habworks/Softcore_SA_P2/Simulation/SPICE/Sallen & Key LPF.asc

C1: cap; 200e-12
C2: cap; 100e-12
C3: cap; 100e-12
C4: cap; 200e-12
D1: diode; 1N4148
D2: diode; 1N4148
R1: res; 220
R2: res; 220
R3: res; 440
R4: res; 100
R5: res; 1K
R6: res; 440
R7: res; 220
R8: res; 220
R10: res; 1K
R11: res; 100
U1: LT1818
U2: ADA4896-2
U3: LT1818
V1: voltage; 3.3V
V2: voltage; SINE(.344 .306 1E5 0 0 0 50); AC 1
V3: voltage; 1.5V
V4: voltage; 1V
Named nets: 0, VCC, VIN, VBUF, VOUT, VOUT_2, VTEST
;tran 10e-5
.ac dec 100 100 10e6
R3 and R6 can be their value or 0.  When sum of input resistors a balance of the input impedance to both + / - terminals.
Otherwise it does not play into circuit calculation
w = 2piF = 1 / SQRT(R1*R2*C1*C2)
Q = SQRT(R1*R2*C1*C2) / (C2(R1 + R2))
Per Stage -40dB/Decade
Per Q = 0.707
Total Roll Off -80dB/Decade
voltage noise per stage = 2.44uV @5MHz
cumulative voltage noise - vector sum = 3.87uV @5MHz
U2 ADA4896 has a wider input Common Mode Voltage range.  
U1 and U3 are cheaper componets but still have a large GBP necessary for filter operation
