habworks/Softcore_SA_P2/Simulation/SPICE/Wien_Bridge_Offset.asc

C1: cap; {Cw}
C2: cap; {Cw}
C3: cap; 10µF
D1: diode; 1N4148
D2: diode; 1N4148
D3: diode; 1N4148
D4: diode; 1N4148
R1: res; 22K
R2: res; {Rw}
R3: res; {Rw}
R4: res; 10K
R5: res; 22K
R6: res; 10K
R7: res; 10K
R8: res; 10K
R9: res; 10K
R10: res; 10K
R11: res; 10K
R12: res; 10K
R13: res; 2.5K
R14: res; 7.5K
R15: res; 10K
U1: ADA4896-2
U2: ADA4896-2
U3: ADA4896-2
U4: AD8606
V1: voltage; 5
V2: voltage; -5
V3: voltage; PULSE(0 .5E-3 0 1E-9 1E-9 1E-4 1E+6 1)
Named nets: VCC, 0, VO_1, VEE, VO_2
.tran 100e-6 uic
.param Rw=200
.param Cw=160pF
V3 is a pulse - necessary to get the ossiclation going.  It would not 
be necessary in a real circuit, but is necessary in a mathematical model due to 
Op Amp modeled too ideal
Capacitors should be ceramic of COG, NP0 type for stability
AD8608 x4 Op Amps
AD8606 x2 Op Amps
AD8605 x1 Op Amp
Double diodes in circuit work to limit out to 2x Vd.  On diode condution R5 in parallel with
R1 to limit gain.  This type of ossicaltor requires a gain of 3 to work.  Without diode circuit
in feedback the ouput would swing to the rails and be clipped creating harmonics
F = 1 / (2*PI*Rw*Cw)
At R = 11K Frequency = 4.384KHz
At R = 1K Frequency = 48.22KHz
.four 48.22k V(VO_2)
AC Analysis - must have:
FFT Analysis done after transient analysis - go to transisent graph and View > FFT
