habworks/Softcore_SA_P2/Simulation/SPICE/Quadrature_Oscillator.asc

C2: cap; .01µF
C3: cap; .01µF
C4: cap; .01µF
R1: res; 100K
R2: res; 100K
R3: res; 100K
R4: res; 100K
U1: TLV9302
U2: TLV9302
V1: voltage; 10
V2: voltage; -10
Named nets: VCC, 0, VOUT, VEE
.tran .2
