habworks/Softcore_SA_P2/Simulation/SPICE/Sallen & Key LPF_Transient.asc

C1: cap; 220e-12
C2: cap; 470e-12
D1: diode; 1N4148
D2: diode; 1N4148
R1: res; 1.5K
R2: res; 1.5K
R3: res; 3K
R4: res; 1K
R5: res; 1K
U1: AD8606
U3: AD8606
V1: voltage; 3.3V
V2: voltage; SINE(1.5 1.5 20e2 0 0 0 10); AC 1
Named nets: 0, VCC, VIN, VOUT
.tran .01
;ac dec 1000 10 2e6
R3 can be 2K or 0.  When 2K it forms a balance of the input impedance to both + / - terminals.
Otherwise it does not play into circuit calculation
w = 2piF = 1 / SQRT(R1*R2*C1*C2)
Q = SQRT(R1*R2*C1*C2) / (C2(R1 + R2)
Reference: https://circuitcellar.com/resources/quickbits/sallen-n-key-filter/
Gain at frequency f
G(f) = 1 / SQRT(1 + f/fc)^2n)
fc = cutoff frequency
n = number of poles (Sallen & Key has 2 poles)
