habworks/Softcore_SA_P2/PS_Softcore_SA/MB_SSA_Platform/microblaze_0/standalone_microblaze_0/bsp/include/xparameters.h

#ifndef XPARAMETERS_H   /* prevent circular inclusions */
#define XPARAMETERS_H   /* by using protection macros */

#define XPAR_XGPIO_NUM_INSTANCES 1

/* Definitions for peripheral AXI_GPIO_0 */
#define XPAR_AXI_GPIO_0_COMPATIBLE "xlnx,axi-gpio-2.0"
#define XPAR_AXI_GPIO_0_BASEADDR 0x40000000
#define XPAR_AXI_GPIO_0_HIGHADDR 0x4000ffff
#define XPAR_AXI_GPIO_0_INTERRUPT_PRESENT 0x0
#define XPAR_AXI_GPIO_0_IS_DUAL 0x1
#define XPAR_AXI_GPIO_0_GPIO_WIDTH 0xc

/* Canonical definitions for peripheral AXI_GPIO_0 */
#define XPAR_XGPIO_0_BASEADDR 0x40000000
#define XPAR_XGPIO_0_HIGHADDR 0x4000ffff
#define XPAR_XGPIO_0_COMPATIBLE "xlnx,axi-gpio-2.0"
#define XPAR_XGPIO_0_GPIO_WIDTH 0xc
#define XPAR_XGPIO_0_INTERRUPT_PRESENT 0x0
#define XPAR_XGPIO_0_IS_DUAL 0x1

#define XPAR_XINTC_NUM_INSTANCES 1

/* Definitions for peripheral AXI_INTC_0 */
#define XPAR_AXI_INTC_0_COMPATIBLE "xlnx,axi-intc-4.1"
#define XPAR_AXI_INTC_0_BASEADDR 0x41200000
#define XPAR_AXI_INTC_0_HIGHADDR 0x4120ffff
#define XPAR_AXI_INTC_0_KIND_OF_INTR 0xf
#define XPAR_AXI_INTC_0_IS_FAST 0x1
#define XPAR_AXI_INTC_0_IVAR_RST_VAL 0x10
#define XPAR_AXI_INTC_0_NUM_INTR_INPUTS 0x4
#define XPAR_AXI_INTC_0_ADDR_WIDTH 0x20
#define XPAR_AXI_INTC_0_OPTIONS 0x0
#define XPAR_AXI_INTC_0_INTCTYPE 0x0
#define XPAR_AXI_INTC_0_HANDLER_TABLE 0x0
#define XPAR_AXI_INTC_0_NUM_SW_INTR 0x0

/* Canonical definitions for peripheral AXI_INTC_0 */
#define XPAR_XINTC_0_BASEADDR 0x41200000
#define XPAR_XINTC_0_HIGHADDR 0x4120ffff
#define XPAR_XINTC_0_HANDLER_TABLE 0x0
#define XPAR_XINTC_0_ADDR_WIDTH 0x20
#define XPAR_XINTC_0_COMPATIBLE "xlnx,axi-intc-4.1"
#define XPAR_XINTC_0_IS_FAST 0x1
#define XPAR_XINTC_0_IVAR_RST_VAL 0x10
#define XPAR_XINTC_0_INTCTYPE 0x0
#define XPAR_XINTC_0_KIND_OF_INTR 0xf
#define XPAR_XINTC_0_NUM_INTR_INPUTS 0x4
#define XPAR_XINTC_0_NUM_SW_INTR 0x0
#define XPAR_XINTC_0_OPTIONS 0x0

#define XPAR_XSPI_NUM_INSTANCES 3

/* Definitions for peripheral AXI_QUAD_SPI_0 */
#define XPAR_AXI_QUAD_SPI_0_COMPATIBLE "xlnx,axi-quad-spi-3.2"
#define XPAR_AXI_QUAD_SPI_0_BASEADDR 0x44a10000
#define XPAR_AXI_QUAD_SPI_0_HIGHADDR 0x44a1ffff
#define XPAR_AXI_QUAD_SPI_0_HASFIFOS 0x1
#define XPAR_AXI_QUAD_SPI_0_SLAVEONLY 0x0
#define XPAR_AXI_QUAD_SPI_0_NUM_SS_BITS 0x4
#define XPAR_AXI_QUAD_SPI_0_BITS_PER_WORD 0x8
#define XPAR_AXI_QUAD_SPI_0_SPI_MODE 0x0
#define XPAR_AXI_QUAD_SPI_0_AXI_INTERFACE 0x0
#define XPAR_AXI_QUAD_SPI_0_AXI4_ADDRESS 0x0
#define XPAR_AXI_QUAD_SPI_0_XIP_MODE 0x0
#define XPAR_AXI_QUAD_SPI_0_STARTUP_BLOCK 0x0
#define XPAR_AXI_QUAD_SPI_0_FIFO_SIZE 0x10

/* Canonical definitions for peripheral AXI_QUAD_SPI_0 */
#define XPAR_XSPI_0_AXI4_ADDRESS 0x0
#define XPAR_XSPI_0_BASEADDR 0x44a10000
#define XPAR_XSPI_0_HIGHADDR 0x44a1ffff
#define XPAR_XSPI_0_AXI_INTERFACE 0x0
#define XPAR_XSPI_0_BITS_PER_WORD 0x8
#define XPAR_XSPI_0_COMPATIBLE "xlnx,axi-quad-spi-3.2"
#define XPAR_XSPI_0_FIFO_SIZE 0x10
#define XPAR_XSPI_0_HASFIFOS 0x1
#define XPAR_XSPI_0_NUM_SS_BITS 0x4
#define XPAR_XSPI_0_SLAVEONLY 0x0
#define XPAR_XSPI_0_SPI_MODE 0x0
#define XPAR_XSPI_0_STARTUP_BLOCK 0x0
#define XPAR_XSPI_0_XIP_MODE 0x0

/* Definitions for peripheral AXI_QUAD_SPI_1 */
#define XPAR_AXI_QUAD_SPI_1_COMPATIBLE "xlnx,axi-quad-spi-3.2"
#define XPAR_AXI_QUAD_SPI_1_BASEADDR 0x44a00000
#define XPAR_AXI_QUAD_SPI_1_HIGHADDR 0x44a0ffff
#define XPAR_AXI_QUAD_SPI_1_HASFIFOS 0x1
#define XPAR_AXI_QUAD_SPI_1_SLAVEONLY 0x0
#define XPAR_AXI_QUAD_SPI_1_NUM_SS_BITS 0x1
#define XPAR_AXI_QUAD_SPI_1_BITS_PER_WORD 0x8
#define XPAR_AXI_QUAD_SPI_1_SPI_MODE 0x0
#define XPAR_AXI_QUAD_SPI_1_AXI_INTERFACE 0x0
#define XPAR_AXI_QUAD_SPI_1_AXI4_ADDRESS 0x0
#define XPAR_AXI_QUAD_SPI_1_XIP_MODE 0x0
#define XPAR_AXI_QUAD_SPI_1_STARTUP_BLOCK 0x0
#define XPAR_AXI_QUAD_SPI_1_FIFO_SIZE 0x10

/* Canonical definitions for peripheral AXI_QUAD_SPI_1 */
#define XPAR_XSPI_1_AXI4_ADDRESS 0x0
#define XPAR_XSPI_1_BASEADDR 0x44a00000
#define XPAR_XSPI_1_HIGHADDR 0x44a0ffff
#define XPAR_XSPI_1_AXI_INTERFACE 0x0
#define XPAR_XSPI_1_BITS_PER_WORD 0x8
#define XPAR_XSPI_1_COMPATIBLE "xlnx,axi-quad-spi-3.2"
#define XPAR_XSPI_1_FIFO_SIZE 0x10
#define XPAR_XSPI_1_HASFIFOS 0x1
#define XPAR_XSPI_1_NUM_SS_BITS 0x1
#define XPAR_XSPI_1_SLAVEONLY 0x0
#define XPAR_XSPI_1_SPI_MODE 0x0
#define XPAR_XSPI_1_STARTUP_BLOCK 0x0
#define XPAR_XSPI_1_XIP_MODE 0x0

/* Definitions for peripheral AXI_QUAD_SPI_2 */
#define XPAR_AXI_QUAD_SPI_2_COMPATIBLE "xlnx,axi-quad-spi-3.2"
#define XPAR_AXI_QUAD_SPI_2_BASEADDR 0x44a40000
#define XPAR_AXI_QUAD_SPI_2_HIGHADDR 0x44a4ffff
#define XPAR_AXI_QUAD_SPI_2_HASFIFOS 0x1
#define XPAR_AXI_QUAD_SPI_2_SLAVEONLY 0x0
#define XPAR_AXI_QUAD_SPI_2_NUM_SS_BITS 0x1
#define XPAR_AXI_QUAD_SPI_2_BITS_PER_WORD 0x8
#define XPAR_AXI_QUAD_SPI_2_SPI_MODE 0x2
#define XPAR_AXI_QUAD_SPI_2_AXI_INTERFACE 0x0
#define XPAR_AXI_QUAD_SPI_2_AXI4_ADDRESS 0x0
#define XPAR_AXI_QUAD_SPI_2_XIP_MODE 0x0
#define XPAR_AXI_QUAD_SPI_2_STARTUP_BLOCK 0x1
#define XPAR_AXI_QUAD_SPI_2_FIFO_SIZE 0x10

/* Canonical definitions for peripheral AXI_QUAD_SPI_2 */
#define XPAR_XSPI_2_AXI4_ADDRESS 0x0
#define XPAR_XSPI_2_BASEADDR 0x44a40000
#define XPAR_XSPI_2_HIGHADDR 0x44a4ffff
#define XPAR_XSPI_2_AXI_INTERFACE 0x0
#define XPAR_XSPI_2_BITS_PER_WORD 0x8
#define XPAR_XSPI_2_COMPATIBLE "xlnx,axi-quad-spi-3.2"
#define XPAR_XSPI_2_FIFO_SIZE 0x10
#define XPAR_XSPI_2_HASFIFOS 0x1
#define XPAR_XSPI_2_NUM_SS_BITS 0x1
#define XPAR_XSPI_2_SLAVEONLY 0x0
#define XPAR_XSPI_2_SPI_MODE 0x2
#define XPAR_XSPI_2_STARTUP_BLOCK 0x1
#define XPAR_XSPI_2_XIP_MODE 0x0

#define XPAR_XTMRCTR_NUM_INSTANCES 4

/* Definitions for peripheral AXI_TIMER_0 */
#define XPAR_AXI_TIMER_0_COMPATIBLE "xlnx,axi-timer-2.0"
#define XPAR_AXI_TIMER_0_BASEADDR 0x41c00000
#define XPAR_AXI_TIMER_0_HIGHADDR 0x41c0ffff
#define XPAR_AXI_TIMER_0_CLOCK_FREQUENCY 0x5f5e100

/* Canonical definitions for peripheral AXI_TIMER_0 */
#define XPAR_XTMRCTR_0_BASEADDR 0x41c00000
#define XPAR_XTMRCTR_0_HIGHADDR 0x41c0ffff
#define XPAR_XTMRCTR_0_COMPATIBLE "xlnx,axi-timer-2.0"
#define XPAR_XTMRCTR_0_CLOCK_FREQUENCY 0x5f5e100

/* Definitions for peripheral AXI_TIMER_1 */
#define XPAR_AXI_TIMER_1_COMPATIBLE "xlnx,axi-timer-2.0"
#define XPAR_AXI_TIMER_1_BASEADDR 0x41c10000
#define XPAR_AXI_TIMER_1_HIGHADDR 0x41c1ffff
#define XPAR_AXI_TIMER_1_CLOCK_FREQUENCY 0x5f5e100
#define XPAR_AXI_TIMER_1_INTERRUPTS 0x2000
#define XPAR_FABRIC_AXI_TIMER_1_INTR 0
#define XPAR_AXI_TIMER_1_INTERRUPT_PARENT 0x41200001

/* Canonical definitions for peripheral AXI_TIMER_1 */
#define XPAR_XTMRCTR_1_BASEADDR 0x41c10000
#define XPAR_FABRIC_XTMRCTR_1_INTR 0
#define XPAR_XTMRCTR_1_HIGHADDR 0x41c1ffff
#define XPAR_XTMRCTR_1_COMPATIBLE "xlnx,axi-timer-2.0"
#define XPAR_XTMRCTR_1_CLOCK_FREQUENCY 0x5f5e100
#define XPAR_XTMRCTR_1_INTERRUPTS 0x2000
#define XPAR_XTMRCTR_1_INTERRUPT_PARENT 0x41200001

/* Definitions for peripheral AXI_TIMER_2 */
#define XPAR_AXI_TIMER_2_COMPATIBLE "xlnx,axi-timer-2.0"
#define XPAR_AXI_TIMER_2_BASEADDR 0x41c20000
#define XPAR_AXI_TIMER_2_HIGHADDR 0x41c2ffff
#define XPAR_AXI_TIMER_2_CLOCK_FREQUENCY 0x5f5e100
#define XPAR_AXI_TIMER_2_INTERRUPTS 0x2001
#define XPAR_FABRIC_AXI_TIMER_2_INTR 1
#define XPAR_AXI_TIMER_2_INTERRUPT_PARENT 0x41200001

/* Canonical definitions for peripheral AXI_TIMER_2 */
#define XPAR_XTMRCTR_2_BASEADDR 0x41c20000
#define XPAR_FABRIC_XTMRCTR_2_INTR 1
#define XPAR_XTMRCTR_2_HIGHADDR 0x41c2ffff
#define XPAR_XTMRCTR_2_COMPATIBLE "xlnx,axi-timer-2.0"
#define XPAR_XTMRCTR_2_CLOCK_FREQUENCY 0x5f5e100
#define XPAR_XTMRCTR_2_INTERRUPTS 0x2001
#define XPAR_XTMRCTR_2_INTERRUPT_PARENT 0x41200001

/* Definitions for peripheral AXI_TIMER_3 */
#define XPAR_AXI_TIMER_3_COMPATIBLE "xlnx,axi-timer-2.0"
#define XPAR_AXI_TIMER_3_BASEADDR 0x41c30000
#define XPAR_AXI_TIMER_3_HIGHADDR 0x41c3ffff
#define XPAR_AXI_TIMER_3_CLOCK_FREQUENCY 0x5f5e100

/* Canonical definitions for peripheral AXI_TIMER_3 */
#define XPAR_XTMRCTR_3_BASEADDR 0x41c30000
#define XPAR_XTMRCTR_3_HIGHADDR 0x41c3ffff
#define XPAR_XTMRCTR_3_COMPATIBLE "xlnx,axi-timer-2.0"
#define XPAR_XTMRCTR_3_CLOCK_FREQUENCY 0x5f5e100

#define XPAR_XUARTLITE_NUM_INSTANCES 1

/* Definitions for peripheral AXI_UARTLITE_0 */
#define XPAR_AXI_UARTLITE_0_COMPATIBLE "xlnx,axi-uartlite-2.0"
#define XPAR_AXI_UARTLITE_0_BASEADDR 0x40600000
#define XPAR_AXI_UARTLITE_0_HIGHADDR 0x4060ffff
#define XPAR_AXI_UARTLITE_0_BAUDRATE 0x1c200
#define XPAR_AXI_UARTLITE_0_USE_PARITY 0x0
#define XPAR_AXI_UARTLITE_0_ODD_PARITY 0x0
#define XPAR_AXI_UARTLITE_0_DATA_BITS 0x8

/* Canonical definitions for peripheral AXI_UARTLITE_0 */
#define XPAR_XUARTLITE_0_BASEADDR 0x40600000
#define XPAR_XUARTLITE_0_HIGHADDR 0x4060ffff
#define XPAR_XUARTLITE_0_BAUDRATE 0x1c200
#define XPAR_XUARTLITE_0_COMPATIBLE "xlnx,axi-uartlite-2.0"
#define XPAR_XUARTLITE_0_DATA_BITS 0x8
#define XPAR_XUARTLITE_0_ODD_PARITY 0x0
#define XPAR_XUARTLITE_0_USE_PARITY 0x0

/* Definitions for peripheral IMR_ADC_7476A_X2_0 */
#define XPAR_IMR_ADC_7476A_X2_0_BASEADDR 0x44a30000
#define XPAR_IMR_ADC_7476A_X2_0_HIGHADDR 0x44a3ffff

/* Canonical definitions for peripheral IMR_ADC_7476A_X2_0 */
#define XPAR_IMR_ADC_7476A_X2_0_BASEADDR 0x44a30000
#define XPAR_IMR_ADC_7476A_X2_0_HIGHADDR 0x44a3ffff

/* Definitions for peripheral IMR_PL_REVISION_0 */
#define XPAR_IMR_PL_REVISION_0_BASEADDR 0x44a20000
#define XPAR_IMR_PL_REVISION_0_HIGHADDR 0x44a2ffff

/* Canonical definitions for peripheral IMR_PL_REVISION_0 */
#define XPAR_IMR_PL_REVISION_0_BASEADDR 0x44a20000
#define XPAR_IMR_PL_REVISION_0_HIGHADDR 0x44a2ffff

#define XPAR_MIG_0_BASEADDRESS 0x80000000
#define XPAR_MIG_0_HIGHADDRESS 0x8fffffff
#define XPAR_LMB_BRAM_0_BASEADDRESS 0x0
#define XPAR_LMB_BRAM_0_HIGHADDRESS 0x1ffff
#define XPAR_CPU_CORE_CLOCK_FREQ_HZ 100000000

#define XPAR_MICROBLAZE_ADDR_SIZE 32

#define XPAR_MICROBLAZE_USE_STACK_PROTECTION 0

/* Number of SLRs */
#define NUMBER_OF_SLRS 0x1

/* Device ID */
#define XPAR_DEVICE_ID "7a100t"

#endif  /* end of protection macro */
