habworks/Softcore_SA_P2/PL_Softcore_SA/PL_Softcore_SA.srcs/sources_1/new/Top.v

`timescale 1ns / 1ps
//////////////////////////////////////////////////////////////////////////////////
// Company: 
// Engineer: 
// 
// Create Date: 12/05/2025 05:24:13 AM
// Design Name: 
// Module Name: Top
// Project Name: 
// Target Devices: 
// Tool Versions: 
// Description: 
// 
// Dependencies: 
// 
// Revision:
// Revision 0.01 - File Created
// Additional Comments:
// 
//////////////////////////////////////////////////////////////////////////////////


module Top(

    );
endmodule
