habworks/Softcore_SA_P2/PS_Softcore_SA/MB_SSA_App/src/Main_Support.h

/******************************************************************************************************
 * @file            Main_Support.h
 * @brief           Header file to support Main_Support.c 
 * ****************************************************************************************************
 * @author          Hab Collector (habco)\n
 *
 * @version         See Main_Support.h: FW_MAJOR_REV, FW_MINOR_REV, FW_TEST_REV
 *
 * @param Development_Environment \n
 * Hardware:        <Xilinx Artix A7> \n
 * IDE:             Vitis 2024.2 \n
 * Compiler:        GCC \n
 * Editor Settings: 1 Tab = 4 Spaces, Recommended Courier New 11
 *
 * @note            The associated header file provides MACRO functions for IO control
 *
 *                  This is an embedded application
 *                  It will be necessary to consult the reference documents to fully understand the code
 *                  It is suggested that the documents be reviewed in the order shown.
 *                    Schematic: 
 *                    IMR Engineering
 *                    IMR Engineering
 *
 * @copyright       IMR Engineering, LLC
 ********************************************************************************************************/

#ifndef MAIN_SUPPORT_H_
#define MAIN_SUPPORT_H_
#ifdef __cplusplus
extern"C" {
#endif

#include <stdint.h>
#include <stdbool.h>
#include <xparameters.h>
#include "xtmrctr.h"
#include "SSD1309_Driver.h"
#include "kiss_fftr.h"


// DEFINES
// PS FW REVSION
#define FW_MAJOR_REV            1
#define FW_MINOR_REV            2
#define FW_TEST_REV             1
#define HW_REV                  1 
// UART USE
#define RX_BUFFER_SIZE          10  
// MICROBLAZE CACHE SUPPORT *** THESE LINES SHOULD BE ADDED WITHIN XPARAMETERS.H BUT THERE IS A BUG IN 2024.2 Vivado / Viits
#define XPAR_MICROBLAZE_USE_ICACHE      1
#define XPAR_MICROBLAZE_USE_DCACHE      1
#define XPAR_MICROBLAZE_USE_MSR_INSTR   1
#define XPAR_MICROBLAZE_ICACHE_BYTE_SIZE 65536  // Value must match MicroBlaze Instruction cache
#define XPAR_MICROBLAZE_DCACHE_BYTE_SIZE 32768  // Value must match MicroBlaze Data cache
// AXI SPI UI CHIP SELECT
#define DISPLAY_CS_NUMBER       ((uint8_t)(0x01 << 0))
#define IOX_1_CS_NUMBER         ((uint8_t)(0x01 << 1))
#define IOX_2_CS_NUMBER         ((uint8_t)(0x01 << 2))
#define AD9833_CS_NUMBER        ((uint8_t)(0x01 << 3))
// IO EXPANDER 1 CONFIGURATION
#define IOX_1_DEVICE_ADDR       ((uint8_t)(0x00))
#define IOX_1_IO_DIRECTION      ((uint8_t)(0x00))
#define IOX_1_INPUT_POLARITY    ((uint8_t)(0x00))
#define IOX_1_IRQ_ON_CHANGE     ((uint8_t)(0x00))
#define IOX_1_IRQ_DEFAULT_VALUE ((uint8_t)(0x00))
#define IOX_1_IRQ_CONTROL       ((uint8_t)(0x00))
#define IOX_1_CONFIGURATION     MCP23S08_SEQOP_BIT_MASK
#define IOX_1_PULLUP            ((uint8_t)(0x00))
// IO EXPANDER 2 CONFIGURATION
#define IOX_2_DEVICE_ADDR       ((uint8_t)(0x01))
#define IOX_2_IO_DIRECTION      ((uint8_t)(0xFF))
#define IOX_2_INPUT_POLARITY    ((uint8_t)(0xC0))   // Two most MSb inputs are active low - so invert
#define IOX_2_IRQ_ON_CHANGE     ((uint8_t)(0xFF))
#define IOX_2_IRQ_DEFAULT_VALUE ((uint8_t)(0x00))
#define IOX_2_IRQ_CONTROL       ((uint8_t)(0x00))
#define IOX_2_CONFIGURATION     (MCP23S08_SEQOP_BIT_MASK | MCP23S08_INTPOL_BIT_MASK)
#define IOX_2_PULLUP            ((uint8_t)(0x00))
// IO EXPANDER 1 OUTPUTS AND ALIAS
#define IOX_1_OUTPUT_0_MASK     ((uint8_t)(0x01 << 0))
#define IOX_1_OUTPUT_1_MASK     ((uint8_t)(0x01 << 1))
#define IOX_1_OUTPUT_2_MASK     ((uint8_t)(0x01 << 2))
#define IOX_1_OUTPUT_3_MASK     ((uint8_t)(0x01 << 3))
#define IOX_1_OUTPUT_4_MASK     ((uint8_t)(0x01 << 4))
#define IOX_1_OUTPUT_5_MASK     ((uint8_t)(0x01 << 5))
#define IOX_1_OUTPUT_6_MASK     ((uint8_t)(0x01 << 6))
#define IOX_1_OUTPUT_7_MASK     ((uint8_t)(0x01 << 7))
#define LED_MODE_SIGNAL         ((uint8_t)(0x01 << 6))
#define LED_MODE_AUDIO          ((uint8_t)(0x01 << 7))
// IO EXPANDER 2 INPUTS AND ALIAS
#define IOX_2_INPUT_0_MASK      ((uint8_t)(0x01 << 0))
#define IOX_2_INPUT_1_MASK      ((uint8_t)(0x01 << 1))
#define IOX_2_INPUT_2_MASK      ((uint8_t)(0x01 << 2))
#define IOX_2_INPUT_3_MASK      ((uint8_t)(0x01 << 3))
#define IOX_2_INPUT_4_MASK      ((uint8_t)(0x01 << 4))
#define IOX_2_INPUT_5_MASK      ((uint8_t)(0x01 << 5))
#define IOX_2_INPUT_6_MASK      ((uint8_t)(0x01 << 6))
#define IOX_2_INPUT_7_MASK      ((uint8_t)(0x01 << 7))
#define UI_SW6_PLAY_HOME        IOX_2_INPUT_0_MASK
#define UI_SW5_PAUSE_AF_TOGGLE  IOX_2_INPUT_1_MASK
#define UI_SW4_STOP_SPAN_TOGGLE IOX_2_INPUT_2_MASK
#define UI_SW3_SELECT           IOX_2_INPUT_3_MASK
#define UI_SW2_MODE             IOX_2_INPUT_4_MASK
#define UI_SW1_FREQ_ADJ_TOGGLE  IOX_2_INPUT_5_MASK
#define UI_SW1_ENCODER_B        IOX_2_INPUT_6_MASK
#define UI_SW1_ENCODER_A        IOX_2_INPUT_7_MASK
// MISC
#define MODE_PERIODIC_IRQ_TIME  0.500                                                   // Value in sec
#define MODE_TIMER_COUNT        (MODE_PERIODIC_IRQ_TIME * XPAR_CPU_CORE_CLOCK_FREQ_HZ)  // Count that lead to Value in sec delay
// FFT RELATED
#define FFT_SAMPLES             1024U
#define FFT_SIZE                FFT_SAMPLES
#ifndef FFT_MAX_BINS
#define FFT_MAX_BINS            ((uint32_t)((FFT_SIZE / 2) + 1))
#endif
#define BIN_COUNT               FFT_MAX_BINS
// ADC RELATED
#define ADC_RESOLUTION_BITS     12U
#define ADC_FULL_SCALE_COUNT    ((1U << ADC_RESOLUTION_BITS) - 1U)   // 4095
#define ADC_MID_SCALE_COUNT     (1U << (ADC_RESOLUTION_BITS - 1U))   // 2048
#define ADC_REF_VOLTAGE         3.3f        


// TYPEDEFS AND ENUMS
typedef enum
{
    MODE_AUDIO_SA = 0,
    MODE_SIGNAL_SA
}Type_Mode;

typedef struct
{
    volatile bool               FrameReady;                 // An FFT size data is ready for processing in the PWM and HannWindow Buffers
    uint16_t                    Size;
    uint32_t                    SampleRate_Hz;
    float                       HannWindow[FFT_SIZE];
    volatile float              Samples[FFT_SIZE];
    float                       RBW;
    kiss_fftr_cfg               FFT_Config;
} Type_FFT;

typedef void (*CS_FunctionPointer)(bool);


// EXTERNS
extern volatile uint32_t volatile ReceivedBytes;
extern volatile uint8_t RxDataBuffer[RX_BUFFER_SIZE];


// MACROS


// FUNCTION PROTOTYPES
void sleep_10us_Wrapper(uint32_t WaitTime);
void sleep_ms_Wrapper(uint32_t WaitTime);
bool SPI_InterfaceTrasmitReceive(XSpi *SPI_UI_Handle, uint8_t ChipSelect_N, uint8_t *TxBuffer, uint8_t *RxBuffer, uint32_t BytesToTransfer, bool UseNegSpiClk, CS_FunctionPointer External_CS_Enable);


#ifdef __cplusplus
}
#endif
#endif /* MAIN_SUPPORT_H_ */
