habworks/Softcore_SA_P2/FPGA_RTL_IP/IMR_ADC_7476A_X2_1_0/hdl/IMR_ADC_7476A_X2_slave_lite_v1_0_S00_AXI.v

`timescale 1 ns / 1 ps

	module IMR_ADC_7476A_X2_slave_lite_v1_0_S00_AXI #
	(
		// Users to add parameters here

		// User parameters ends
		// Do not modify the parameters beyond this line

		// Width of S_AXI data bus
		parameter integer C_S_AXI_DATA_WIDTH	= 32,
		// Width of S_AXI address bus
		parameter integer C_S_AXI_ADDR_WIDTH	= 5
	)
	(
		// Users to add ports here
		// ADC port interface
		output wire ADC_SCLK,
		output wire ADC_CS_n,
		input  wire ADC_MISO_A,
		input  wire ADC_MISO_B,
		output wire IRQ,
		// User ports ends
		// Do not modify the ports beyond this line

		// Global Clock Signal
		input wire  S_AXI_ACLK,
		// Global Reset Signal. This Signal is Active LOW
		input wire  S_AXI_ARESETN,
		// Write address (issued by master, acceped by Slave)
		input wire [C_S_AXI_ADDR_WIDTH-1 : 0] S_AXI_AWADDR,
		// Write channel Protection type. This signal indicates the
    		// privilege and security level of the transaction, and whether
    		// the transaction is a data access or an instruction access.
		input wire [2 : 0] S_AXI_AWPROT,
		// Write address valid. This signal indicates that the master signaling
    		// valid write address and control information.
		input wire  S_AXI_AWVALID,
		// Write address ready. This signal indicates that the slave is ready
    		// to accept an address and associated control signals.
		output wire  S_AXI_AWREADY,
		// Write data (issued by master, acceped by Slave) 
		input wire [C_S_AXI_DATA_WIDTH-1 : 0] S_AXI_WDATA,
		// Write strobes. This signal indicates which byte lanes hold
    		// valid data. There is one write strobe bit for each eight
    		// bits of the write data bus.    
		input wire [(C_S_AXI_DATA_WIDTH/8)-1 : 0] S_AXI_WSTRB,
		// Write valid. This signal indicates that valid write
    		// data and strobes are available.
		input wire  S_AXI_WVALID,
		// Write ready. This signal indicates that the slave
    		// can accept the write data.
		output wire  S_AXI_WREADY,
		// Write response. This signal indicates the status
    		// of the write transaction.
		output wire [1 : 0] S_AXI_BRESP,
		// Write response valid. This signal indicates that the channel
    		// is signaling a valid write response.
		output wire  S_AXI_BVALID,
		// Response ready. This signal indicates that the master
    		// can accept a write response.
		input wire  S_AXI_BREADY,
		// Read address (issued by master, acceped by Slave)
		input wire [C_S_AXI_ADDR_WIDTH-1 : 0] S_AXI_ARADDR,
		// Protection type. This signal indicates the privilege
    		// and security level of the transaction, and whether the
    		// transaction is a data access or an instruction access.
		input wire [2 : 0] S_AXI_ARPROT,
		// Read address valid. This signal indicates that the channel
    		// is signaling valid read address and control information.
		input wire  S_AXI_ARVALID,
		// Read address ready. This signal indicates that the slave is
    		// ready to accept an address and associated control signals.
		output wire  S_AXI_ARREADY,
		// Read data (issued by slave)
		output wire [C_S_AXI_DATA_WIDTH-1 : 0] S_AXI_RDATA,
		// Read response. This signal indicates the status of the
    		// read transfer.
		output wire [1 : 0] S_AXI_RRESP,
		// Read valid. This signal indicates that the channel is
    		// signaling the required read data.
		output wire  S_AXI_RVALID,
		// Read ready. This signal indicates that the master can
    		// accept the read data and response information.
		input wire  S_AXI_RREADY
	);

	// AXI4LITE signals
	reg [C_S_AXI_ADDR_WIDTH-1 : 0] 	axi_awaddr;
	reg  	axi_awready;
	reg  	axi_wready;
	reg [1 : 0] 	axi_bresp;
	reg  	axi_bvalid;
	reg [C_S_AXI_ADDR_WIDTH-1 : 0] 	axi_araddr;
	reg  	axi_arready;
	reg [1 : 0] 	axi_rresp;
	reg  	axi_rvalid;

	// Example-specific design signals
	// local parameter for addressing 32 bit / 64 bit C_S_AXI_DATA_WIDTH
	// ADDR_LSB is used for addressing 32/64 bit registers/memories
	// ADDR_LSB = 2 for 32 bits (n downto 2)
	// ADDR_LSB = 3 for 64 bits (n downto 3)
	localparam integer ADDR_LSB = (C_S_AXI_DATA_WIDTH/32) + 1;
	localparam integer OPT_MEM_ADDR_BITS = 3; // Hab consider making this a global parameter
	//----------------------------------------------
	//-- Signals for user logic register space example
	//------------------------------------------------
	//-- Number of Slave Registers 5
	reg [C_S_AXI_DATA_WIDTH-1:0]	slv_reg0;
	wire [C_S_AXI_DATA_WIDTH-1:0]	slv_reg1;
	wire [C_S_AXI_DATA_WIDTH-1:0]	slv_reg2;
	wire [C_S_AXI_DATA_WIDTH-1:0]	slv_reg3;
	reg [C_S_AXI_DATA_WIDTH-1:0]	slv_reg4;
	integer	 byte_index;

	// I/O Connections assignments
	assign S_AXI_AWREADY	= axi_awready;
	assign S_AXI_WREADY	= axi_wready;
	assign S_AXI_BRESP	= axi_bresp;
	assign S_AXI_BVALID	= axi_bvalid;
	assign S_AXI_ARREADY	= axi_arready;
	assign S_AXI_RRESP	= axi_rresp;
	assign S_AXI_RVALID	= axi_rvalid;
	 //state machine varibles 
	 reg [1:0] state_write;
	 reg [1:0] state_read;
	 //State machine local parameters
	 localparam Idle = 2'b00,Raddr = 2'b10,Rdata = 2'b11 ,Waddr = 2'b10,Wdata = 2'b11;

	 
	// Implement Write state machine
	// Outstanding write transactions are not supported by the slave i.e., master should assert bready to receive response on or before it starts sending the new transaction
	//======================================================
    // AXI Write Channel FSM
    // Handles AXI-Lite write handshakes:
    // - Waits for valid address/data from master
    // - Latches write address
    // - Generates write response (OKAY)
    // - Controls ready/valid signals per AXI protocol
    //======================================================
    //
    // USER MUST AUGMENT AS SUCH:
    // - Normally no edits required; FSM handles AXI protocol
    // - Verify axi_bresp is set to OKAY (2'b00) for successful writes
    // - Optionally add error response handling if invalid addresses should fault
	always @(posedge S_AXI_ACLK)                                 
	  begin                                 
	     if (S_AXI_ARESETN == 1'b0)                                 
	       begin                                 
	         axi_awready <= 0;                                 
	         axi_wready <= 0;                                 
	         axi_bvalid <= 0;                                 
	         axi_bresp <= 0;                                 
	         axi_awaddr <= 0;                                 
	         state_write <= Idle;                                 
	       end                                 
	     else                                  
	       begin                                 
	         case(state_write)                                 
	           Idle:                                      
	             begin                                 
	               if(S_AXI_ARESETN == 1'b1)                                  
	                 begin                                 
	                   axi_awready <= 1'b1;                                 
	                   axi_wready <= 1'b1;                                 
	                   state_write <= Waddr;                                 
	                 end                                 
	               else state_write <= state_write;                                 
	             end                                 
	           Waddr:        //At this state, slave is ready to receive address along with corresponding control signals and first data packet. Response valid is also handled at this state                                 
	             begin                                 
	               if (S_AXI_AWVALID && S_AXI_AWREADY)                                 
	                  begin                                 
	                    axi_awaddr <= S_AXI_AWADDR;                                 
	                    if(S_AXI_WVALID)                                  
	                      begin                                   
	                        axi_awready <= 1'b1;                                 
	                        state_write <= Waddr;                                 
	                        axi_bvalid <= 1'b1;                                 
	                      end                                 
	                    else                                  
	                      begin                                 
	                        axi_awready <= 1'b0;                                 
	                        state_write <= Wdata;                                 
	                        if (S_AXI_BREADY && axi_bvalid) axi_bvalid <= 1'b0;                                 
	                      end                                 
	                  end                                 
	               else                                  
	                  begin                                 
	                    state_write <= state_write;                                 
	                    if (S_AXI_BREADY && axi_bvalid) axi_bvalid <= 1'b0;                                 
	                   end                                 
	             end                                 
	          Wdata:        //At this state, slave is ready to receive the data packets until the number of transfers is equal to burst length                                 
	             begin                                 
	               if (S_AXI_WVALID)                                 
	                 begin                                 
	                   state_write <= Waddr;                                 
	                   axi_bvalid <= 1'b1;                                 
	                   axi_awready <= 1'b1;                                 
	                 end                                 
	                else                                  
	                 begin                                 
	                   state_write <= state_write;                                 
	                   if (S_AXI_BREADY && axi_bvalid) axi_bvalid <= 1'b0;                                 
	                 end                                              
	             end                                 
	          endcase                                 
	        end                                 
	      end                                 


	// Implement memory mapped register select and write logic generation
	// The write data is accepted and written to memory mapped registers when
	// axi_awready, S_AXI_WVALID, axi_wready and S_AXI_WVALID are asserted. Write strobes are used to
	// select byte enables of slave registers while writing.
	// These registers are cleared when reset (active low) is applied.
	// Slave register write enable is asserted when valid address and data are available
	// and the slave is ready to accept the write address and write data.
    //======================================================
    // AXI Write Data Path (Register File Update)
    // - Clears all slave registers on reset
    // - On valid write transaction, decodes address
    // - Updates the selected slave register (slv_reg0..slv_reg4)
    // - Applies byte-enable masking with WSTRB
    //======================================================
    //
    // USER MUST AUGMENT AS SUCH:
    // - Map slv_reg0..4 to functional registers (CTRL, STATUS, DATAA, DATAB, IRQ_EN, etc.)
    // - Prevent writes to read-only regs (STATUS, DATAA, DATAB)
    // - Add side-effects for CTRL writes (e.g., Start pulse, SoftRst self-clear)
    // - Expand address decode (OPT_MEM_ADDR_BITS) if more registers are required	 
	always @( posedge S_AXI_ACLK )
	begin
	  if ( S_AXI_ARESETN == 1'b0 )
	    begin
	      slv_reg0 <= 0;
	    //   slv_reg1 <= 0;
	    //   slv_reg2 <= 0;
	    //   slv_reg3 <= 0;
	      slv_reg4 <= 0;
	    end 
	  else begin
	    if (S_AXI_WVALID)
	      begin
	        case ( (S_AXI_AWVALID) ? S_AXI_AWADDR[ADDR_LSB+OPT_MEM_ADDR_BITS-1:ADDR_LSB] : axi_awaddr[ADDR_LSB+OPT_MEM_ADDR_BITS-1:ADDR_LSB] )
	          3'h0:
	            for ( byte_index = 0; byte_index <= (C_S_AXI_DATA_WIDTH/8)-1; byte_index = byte_index+1 )
	              if ( S_AXI_WSTRB[byte_index] == 1 ) begin
	                // Respective byte enables are asserted as per write strobes 
	                // Slave register 0
	                slv_reg0[(byte_index*8) +: 8] <= S_AXI_WDATA[(byte_index*8) +: 8];
	              end  
	          3'h1:
	            for ( byte_index = 0; byte_index <= (C_S_AXI_DATA_WIDTH/8)-1; byte_index = byte_index+1 )
	              if ( S_AXI_WSTRB[byte_index] == 1 ) begin
	                // Respective byte enables are asserted as per write strobes 
	                // Slave register 1
	                // slv_reg1[(byte_index*8) +: 8] <= S_AXI_WDATA[(byte_index*8) +: 8]; Hab comment out to make read-only
	              end  
	          3'h2:
	            for ( byte_index = 0; byte_index <= (C_S_AXI_DATA_WIDTH/8)-1; byte_index = byte_index+1 )
	              if ( S_AXI_WSTRB[byte_index] == 1 ) begin
	                // Respective byte enables are asserted as per write strobes 
	                // Slave register 2
	                // slv_reg2[(byte_index*8) +: 8] <= S_AXI_WDATA[(byte_index*8) +: 8];
	              end  
	          3'h3:
	            for ( byte_index = 0; byte_index <= (C_S_AXI_DATA_WIDTH/8)-1; byte_index = byte_index+1 )
	              if ( S_AXI_WSTRB[byte_index] == 1 ) begin
	                // Respective byte enables are asserted as per write strobes 
	                // Slave register 3
	                // slv_reg3[(byte_index*8) +: 8] <= S_AXI_WDATA[(byte_index*8) +: 8]; 
	              end  
	          3'h4:
	            for ( byte_index = 0; byte_index <= (C_S_AXI_DATA_WIDTH/8)-1; byte_index = byte_index+1 )
	              if ( S_AXI_WSTRB[byte_index] == 1 ) begin
	                // Respective byte enables are asserted as per write strobes 
	                // Slave register 4
	                slv_reg4[(byte_index*8) +: 8] <= S_AXI_WDATA[(byte_index*8) +: 8];
				  end
	          default : begin
	                      slv_reg0 <= slv_reg0;
	                    //   slv_reg1 <= slv_reg1;
	                    //   slv_reg2 <= slv_reg2;
	                    //   slv_reg3 <= slv_reg3;
	                      slv_reg4 <= slv_reg4;
	                    end
	        endcase
	      end
	  end
	end    

	// Hab Added this always block to self-clear IRQ Clear bit if set outside of write
	// always @(posedge S_AXI_ACLK)
	// begin
	//   if ( S_AXI_ARESETN == 1'b0 ) begin
	//       slv_reg4[1] <= 1'b0; // Clear IRQ Clear bit on reset
	//   end else begin
	//       if (slv_reg4[1]) begin
	//           slv_reg4[1] <= 1'b0; // Clear IRQ Clear bit after write
	//       end
	//   end
	// end

	// Hab Added this always block to self-clear Control Start bit if set outside of write
	// reg StartBitDelay;
	// always @(posedge S_AXI_ACLK)
	// begin
	//   if ( S_AXI_ARESETN == 1'b0 ) 
	//   begin
	//       slv_reg0[1] <= 1'b0; // Clear IRQ Clear bit on reset
	// 	  StartBitDelay <= 1'b0;
	//   end
	//   else 
	//   begin
	//   	StartBitDelay <= slv_reg0[1];
	// 	if (StartBitDelay)
	// 	begin
	//           slv_reg0[1] <= 1'b0; // Clear IRQ Clear bit after write
	// 		  StartBitDelay <= 1'b0;
	// 	end
	//   end
	// end


	// Implement read state machine
	//======================================================
    // AXI Read Channel FSM
    // - Implements AXI-Lite read address/data handshakes
    // - Waits for valid read address from master
    // - Latches read address
    // - Asserts read valid and provides response (OKAY)
    // - Completes handshake when master accepts data
    //======================================================
    //
    // USER MUST AUGMENT AS SUCH:
    // - Normally no edits required; FSM handles AXI protocol
    // - Verify axi_rresp is set to OKAY (2'b00) for successful reads
    // - Ensure read data path (separate mux logic) is updated to map
    //   slv_reg0..4 to functional registers (CTRL, STATUS, DATAA, DATAB, IRQ_EN)
    // - Add side-effects as needed (e.g., clear DataRdy on read of DATAA)
	  always @(posedge S_AXI_ACLK)                                       
	    begin                                       
	      if (S_AXI_ARESETN == 1'b0)                                       
	        begin                                       
	         //asserting initial values to all 0's during reset                                       
	         axi_arready <= 1'b0;                                       
	         axi_rvalid <= 1'b0;                                       
	         axi_rresp <= 1'b0;                                       
	         state_read <= Idle;                                       
	        end                                       
	      else                                       
	        begin                                       
	          case(state_read)                                       
	            Idle:     //Initial state inidicating reset is done and ready to receive read/write transactions                                       
	              begin                                                
	                if (S_AXI_ARESETN == 1'b1)                                        
	                  begin                                       
	                    state_read <= Raddr;                                       
	                    axi_arready <= 1'b1;                                       
	                  end                                       
	                else state_read <= state_read;                                       
	              end                                       
	            Raddr:        //At this state, slave is ready to receive address along with corresponding control signals                                       
	              begin                                       
	                if (S_AXI_ARVALID && S_AXI_ARREADY)                                       
	                  begin                                       
	                    state_read <= Rdata;                                       
	                    axi_araddr <= S_AXI_ARADDR;                                       
	                    axi_rvalid <= 1'b1;                                       
	                    axi_arready <= 1'b0;                                       
	                  end                                       
	                else state_read <= state_read;                                       
	              end                                       
	            Rdata:        //At this state, slave is ready to send the data packets until the number of transfers is equal to burst length                                       
	              begin                                           
	                if (S_AXI_RVALID && S_AXI_RREADY)                                       
	                  begin                                       
	                    axi_rvalid <= 1'b0;                                       
	                    axi_arready <= 1'b1;                                       
	                    state_read <= Raddr;                                       
	                  end                                       
	                else state_read <= state_read;                                       
	              end                                       
	           endcase                                       
	          end                                       
	        end                                         
	// Implement memory mapped register select and read logic generation
	  assign S_AXI_RDATA = (axi_araddr[ADDR_LSB+OPT_MEM_ADDR_BITS-1:ADDR_LSB] == 3'h0) ? slv_reg0 : (axi_araddr[ADDR_LSB+OPT_MEM_ADDR_BITS-1:ADDR_LSB] == 3'h1) ? slv_reg1 : (axi_araddr[ADDR_LSB+OPT_MEM_ADDR_BITS-1:ADDR_LSB] == 3'h2) ? slv_reg2 : (axi_araddr[ADDR_LSB+OPT_MEM_ADDR_BITS-1:ADDR_LSB] == 3'h3) ? slv_reg3 : (axi_araddr[ADDR_LSB+OPT_MEM_ADDR_BITS-1:ADDR_LSB] == 3'h4) ? slv_reg4 : 0; 
	// Add user logic here
	IMR_ADC_7476A_X2_Core u_adc_core 
	(
		// Clock / Reset
		.SysClk(S_AXI_ACLK),
		.RST_n(S_AXI_ARESETN),

		// Control + IRQ enable from AXI regs
		.Ctrl_Register(slv_reg0),
		.IRQ_Register(slv_reg4),

		// Readback to AXI (STATUS / DATA_A / DATA_B)
		.Status_Register(slv_reg1),
		.ADC_Data_A_Register(slv_reg2),
		.ADC_Data_B_Register(slv_reg3),

		// External ADC pins
		.MISO_A(ADC_MISO_A),
		.MISO_B(ADC_MISO_B),
		.SCLK(ADC_SCLK),
		.CS_n(ADC_CS_n),

		// Interrupt to system
		.IP_IRQ(IRQ)
	);
	// User logic ends

	endmodule
