habworks/Softcore_SA_P2/Bootloader_Softcore_SA/MB_SSA_BL_App/src/blconfig.h

/******************************************************************************
* Copyright (C) 2004 - 2020 Xilinx, Inc.  All rights reserved.
* Copyright (C) 2024 Advanced Micro Devices, Inc.  All rights reserved.
* SPDX-License-Identifier: MIT
******************************************************************************/
#ifdef __cplusplus
extern "C" {
#endif
#warning "Please provide the correct address value for the definition FLASH_IMAGE_BASEADDR. Please give the flash offset @ which SREC application is programmed"

#define FLASH_IMAGE_BASEADDR  0x00500000
// PS FW REVSION
#define FW_MAJOR_REV            1
#define FW_MINOR_REV            1
#define FW_TEST_REV             0
#define HW_REV                  1

#ifdef __cplusplus
}
#endif
